hwoiz/TonMOBIL/STL-Dateien/Gehäuse/5V.stl

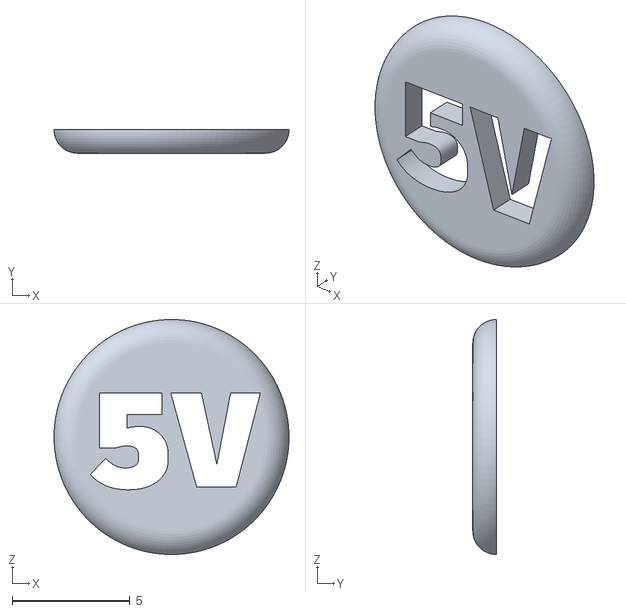
[picture p55: CAD file, 2021-07-15]
STL-Dateien/Gehäuse/5V.stl
10.00 x 1.00 x 10.00
