hwoiz/TonMOBIL/STL-Dateien/NFC-Tiere/Eichhörnchen-Boden.stl

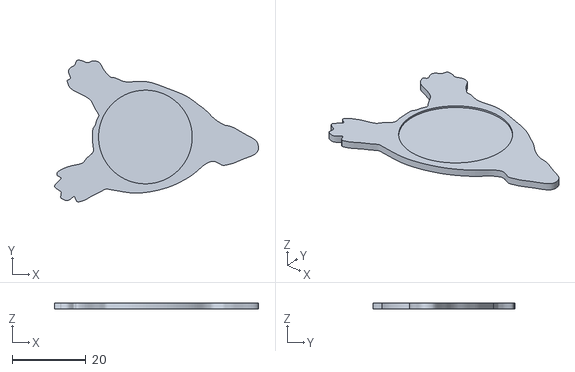
[picture p56: CAD file, 2021-07-26]
STL-Dateien/NFC-Tiere/Eichhörnchen-Boden.stl
55.3 x 38.5 x 1.60
