hwoiz/TonMOBIL/STL-Dateien/Gehäuse/Rückteil.stl

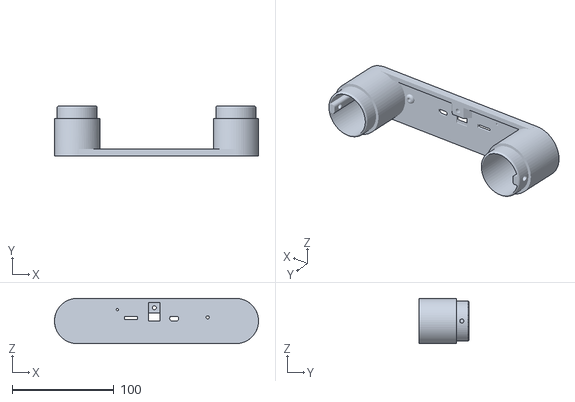
[picture p57: CAD file, 2021-07-15]
STL-Dateien/Gehäuse/Rückteil.stl
200.5 x 49.0 x 44.5
