hwoiz/TonMOBIL/STL-Dateien/NFC-Tiere/Katze.stl

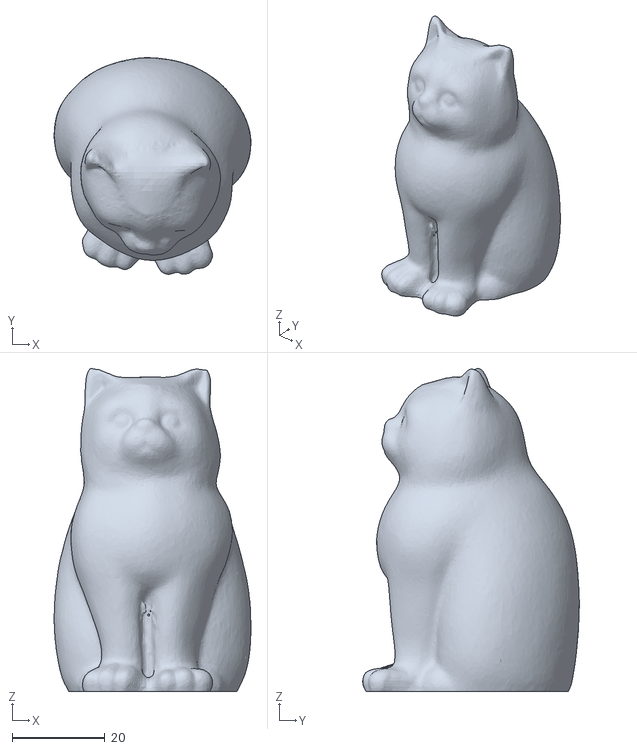
[picture p58: CAD file, 2021-07-26]
STL-Dateien/NFC-Tiere/Katze.stl
42.5 x 46.8 x 69.7
