hwoiz/TonMOBIL/STL-Dateien/Gehäuse/Vorderteil.stl

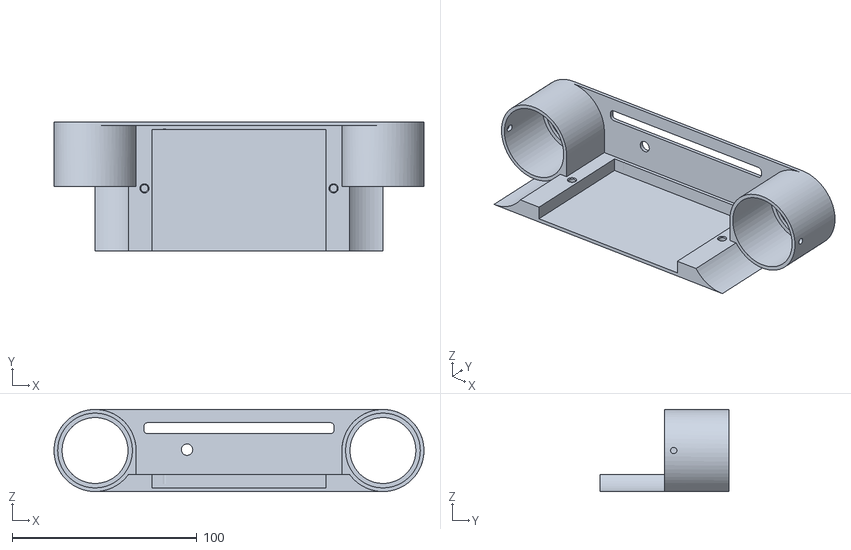
[picture p59: CAD file, 2021-07-15]
STL-Dateien/Gehäuse/Vorderteil.stl
200.5 x 70.0 x 44.5
