hwoiz/TonMOBIL/STL-Dateien/NFC-Tiere/Frosch-Boden.stl

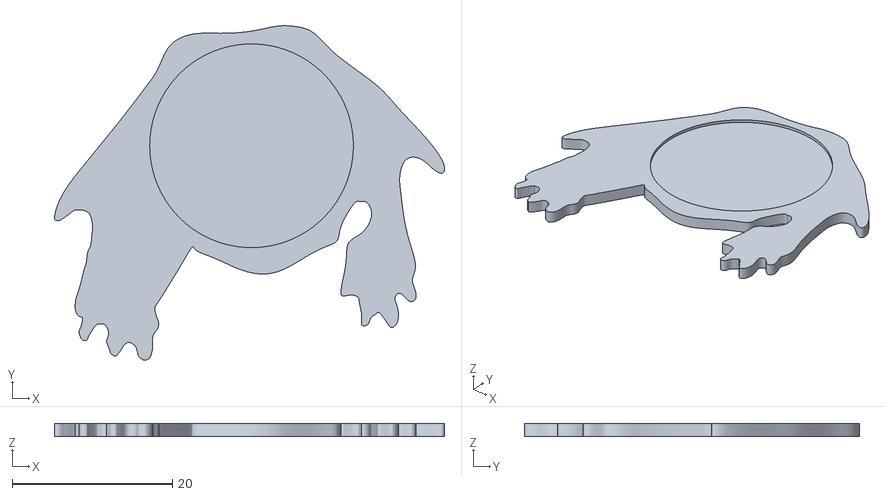
[picture p60: CAD file, 2021-07-26]
STL-Dateien/NFC-Tiere/Frosch-Boden.stl
48.6 x 41.7 x 1.60
