hwoiz/TonMOBIL/STL-Dateien/Gehäuse/Logo.stl

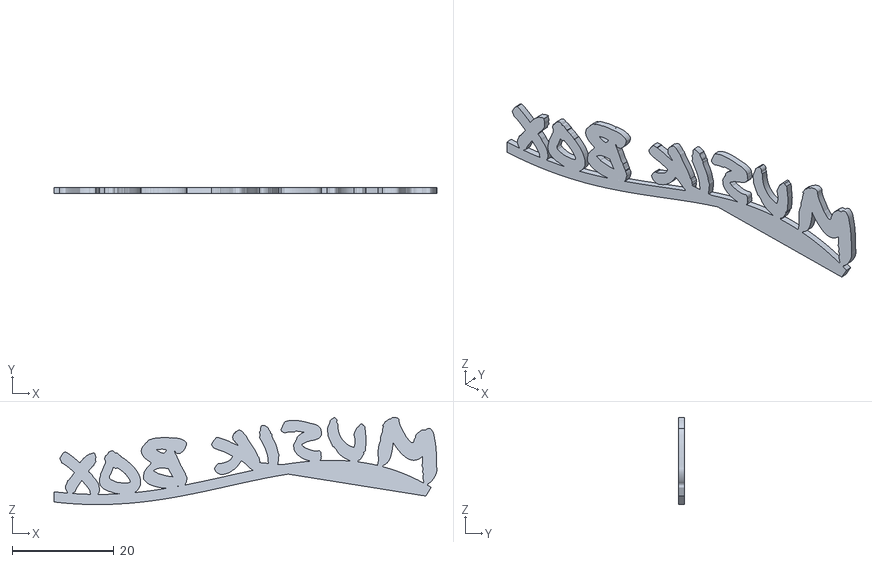
[picture p61: CAD file, 2021-07-15]
STL-Dateien/Gehäuse/Logo.stl
75.2 x 1.20 x 17.1
