hwoiz/TonMOBIL/STL-Dateien/NFC-Tiere/Hase.stl

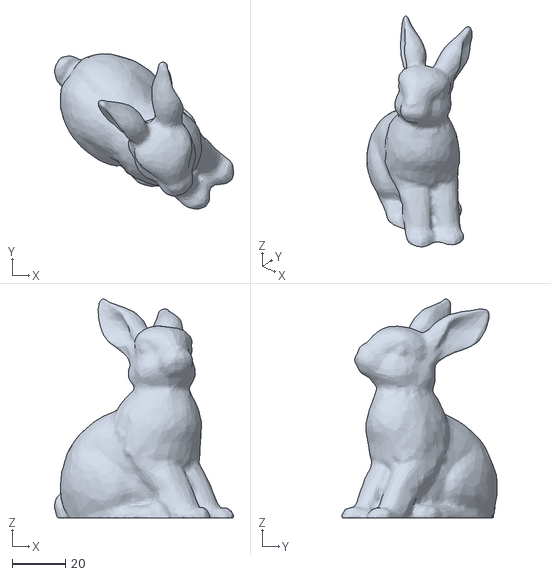
[picture p62: CAD file, 2021-07-26]
STL-Dateien/NFC-Tiere/Hase.stl
67.3 x 58.3 x 82.2
