hwoiz/TonMOBIL/STL-Dateien/Gehäuse/Gitter.stl

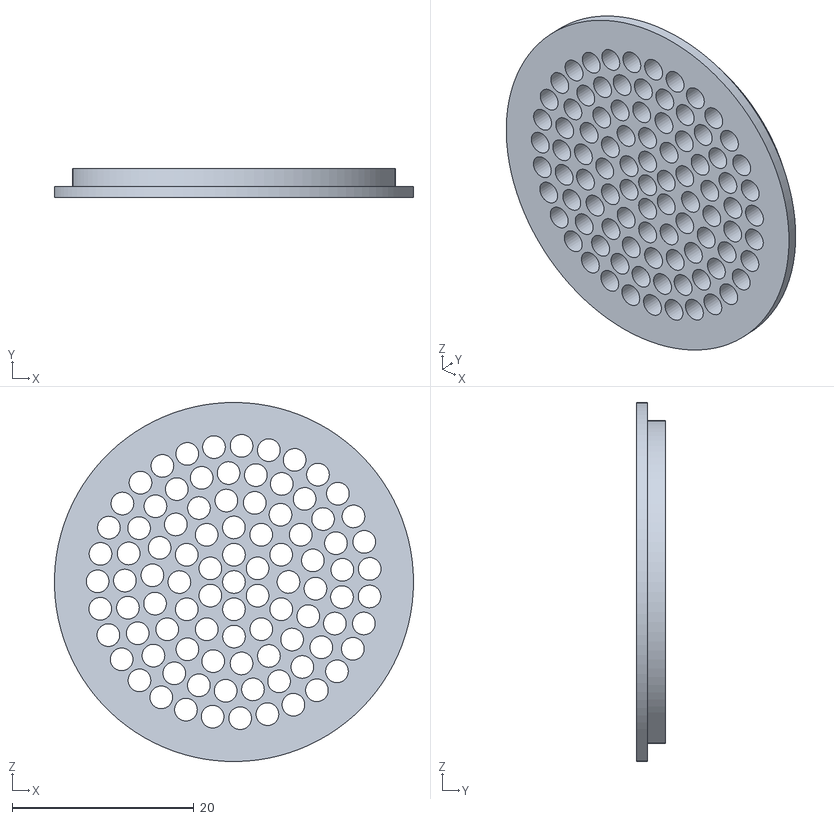
[picture p63: CAD file, 2021-07-15]
STL-Dateien/Gehäuse/Gitter.stl
39.5 x 3.20 x 39.5
