hwoiz/TonMOBIL/STL-Dateien/NFC-Tiere/Katze-Boden.stl

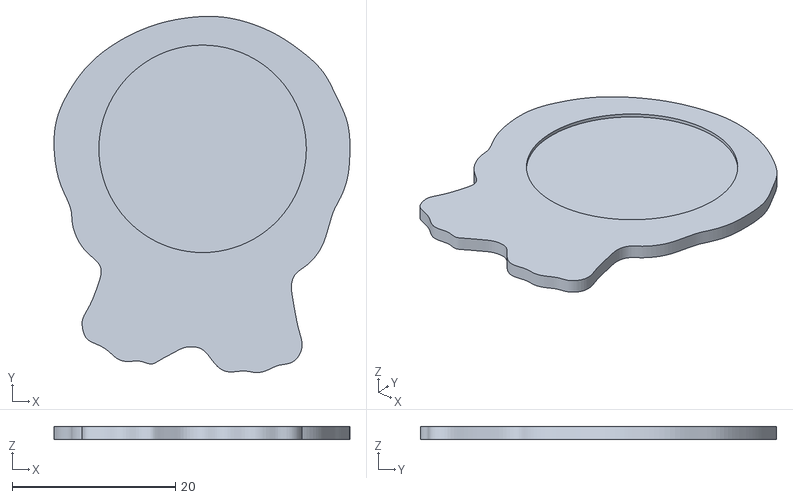
[picture p64: CAD file, 2021-07-26]
STL-Dateien/NFC-Tiere/Katze-Boden.stl
36.2 x 43.6 x 1.60
