hwoiz/TonMOBIL/STL-Dateien/Gehäuse/Firmware-Deckel.stl

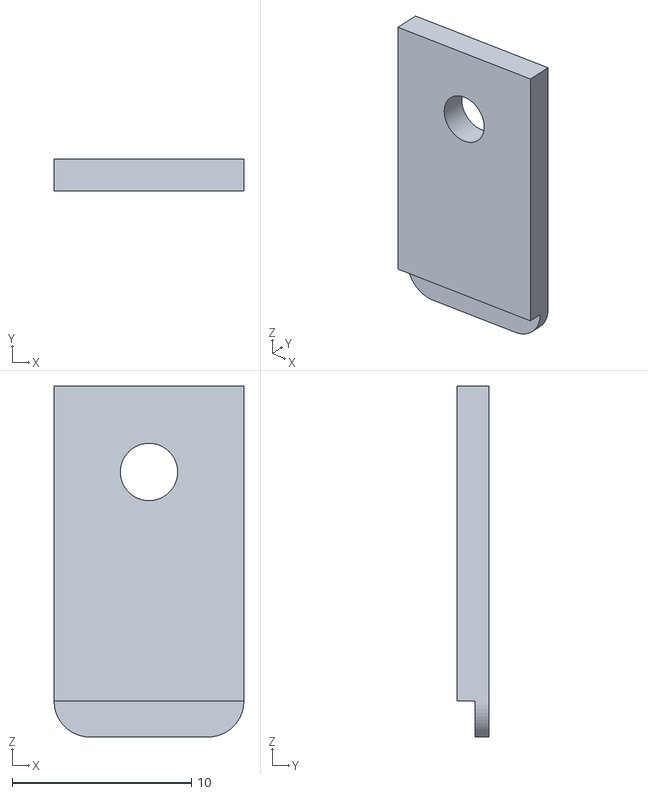
[picture p65: CAD file, 2021-07-15]
STL-Dateien/Gehäuse/Firmware-Deckel.stl
10.6 x 1.80 x 19.6
