hwoiz/TonMOBIL/STL-Dateien/NFC-Tiere/Hase-Boden.stl

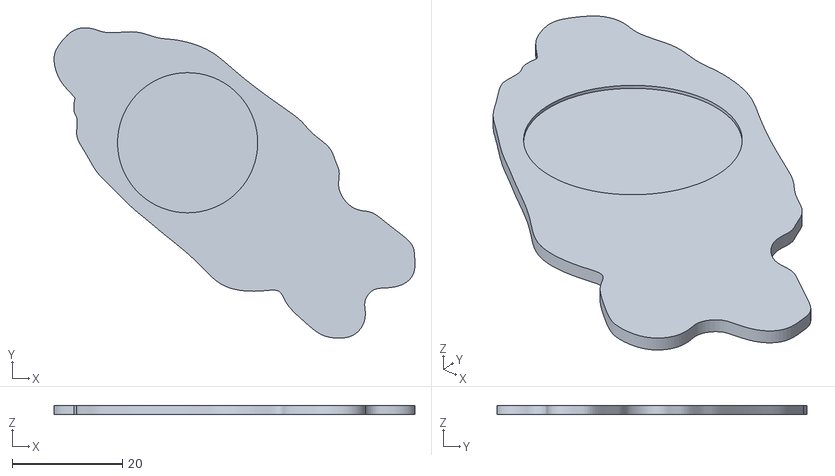
[picture p66: CAD file, 2021-07-26]
STL-Dateien/NFC-Tiere/Hase-Boden.stl
65.4 x 56.3 x 1.60
