hwoiz/TonMOBIL/STL-Dateien/Gehäuse/NFC_Switch-Halter.stl

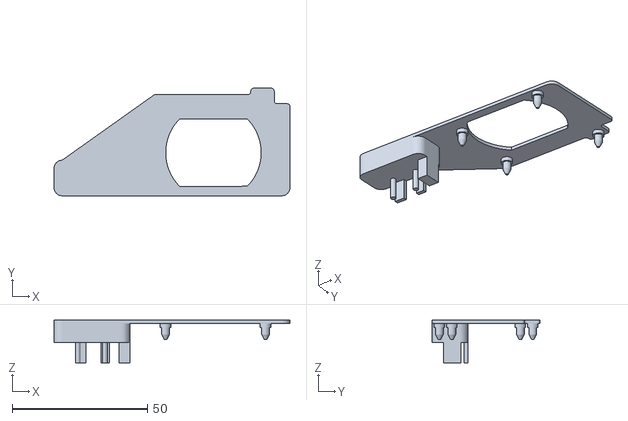
[picture p67: CAD file, 2021-07-15]
STL-Dateien/Gehäuse/NFC_Switch-Halter.stl
87.1 x 39.7 x 15.7
