hwoiz/TonMOBIL/STL-Dateien/NFC-Tiere/Bär-Boden.stl

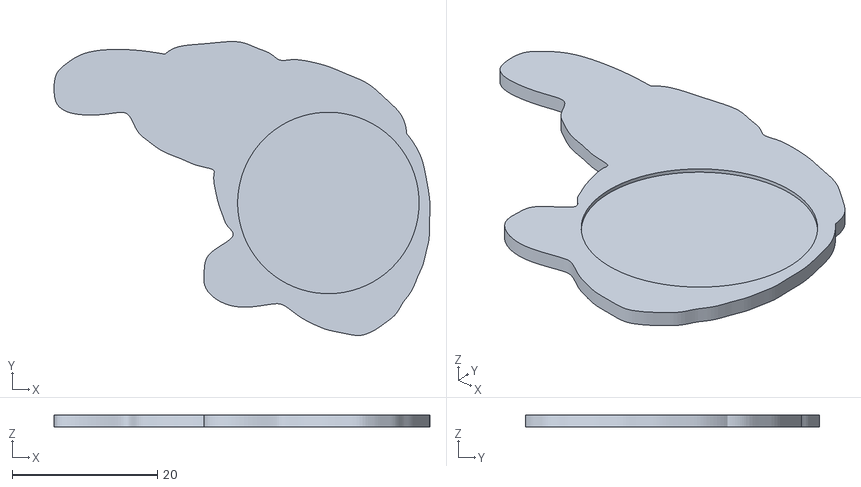
[picture p68: CAD file, 2021-07-26]
STL-Dateien/NFC-Tiere/Bär-Boden.stl
51.8 x 40.5 x 1.60
