hwoiz/TonMOBIL/STL-Dateien/NFC-Tiere/Hund.stl

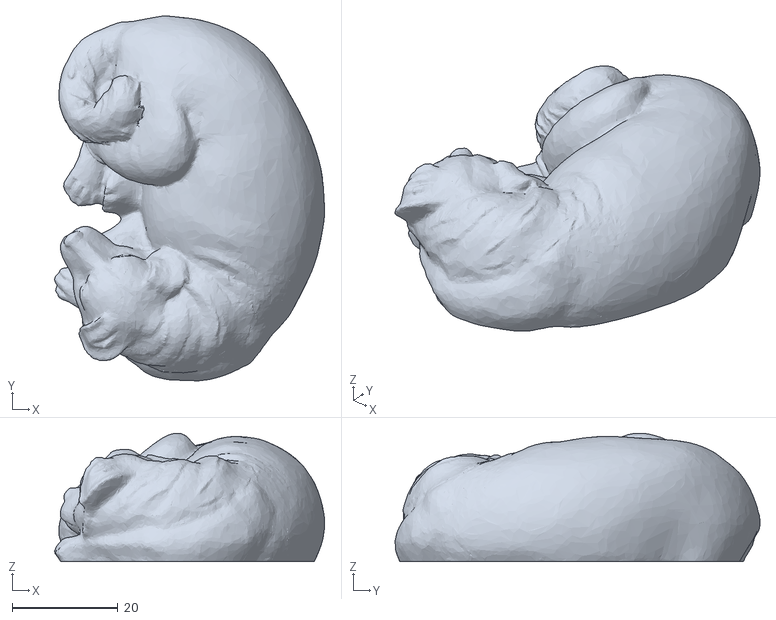
[picture p69: CAD file, 2021-07-26]
STL-Dateien/NFC-Tiere/Hund.stl
51.0 x 69.0 x 24.3
